dchwebb/DisPhaze/DisPhazePoly/src/LUT.cpp

#include "LUT.h"
#include "Calib.h"

extern Config config;

// Create phase distortion look up tables
const float PDSquareLUT[pdLutSize] = {0,0.000182,0.000446,0.000789,0.001206,0.001693,0.002248,0.002868,0.003549,0.004290,0.005087,0.005938,0.006841,0.007794,0.008795,0.009843,0.010935,0.012072,0.013250,0.014470,0.015730,0.017029,0.018366,0.019742,0.021155,0.022605,0.024091,0.025615,0.027175,0.028771,0.030405,0.032076,0.033786,0.035534,0.037322,0.039150,0.041021,0.042935,0.044895,0.046903,0.048960,0.051070,0.053237,0.055463,0.057754,0.060114,0.062551,0.065071,0.067684,0.070402,0.073238,0.082960,0.092174,0.100907,0.109182,0.117021,0.124446,0.131478,0.138135,0.144436,0.150398,0.156039,0.161373,0.166417,0.171183,0.175687,0.179939,0.183954,0.187742,0.191315,0.194682,0.197855,0.200842,0.203653,0.206296,0.208779,0.211110,0.213297,0.215346,0.217264,0.219058,0.220733,0.222295,0.223750,0.225102,0.226357,0.227520,0.228594,0.229584,0.230495,0.231329,0.232090,0.232783,0.233410,0.233974,0.234478,0.234926,0.235319,0.235660,0.235953,0.236198,0.236399,0.236557,0.236674,0.236753,0.236794,0.236800,0.236773,0.236713,0.236623,0.236503,0.236356,0.236182,0.235982,0.235758,0.235511,0.235242,0.234951,0.234640,0.234310,0.233961,0.233595,0.233211,0.232812,0.232396,0.231966,0.231522,0.231064,0.230593,0.230109,0.229614,0.229107,0.228589,0.228060,0.227521,0.226973,0.226415,0.225848,0.225272,0.224688,0.224096,0.223497,0.222890,0.222276,0.221655,0.221028,0.220394,0.219754,0.219108,0.218456,0.217799,0.217137,0.216469,0.215797,0.215120,0.214438,0.213751,0.213061,0.212366,0.211667,0.210964,0.210257,0.209547,0.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
9737,-0.060073,-0.060292,-0.060402,-0.060410,-0.060325,-0.060151,-0.059895,-0.059562,-0.059159,-0.058690,-0.058159,-0.057571,-0.056930,-0.056239,-0.055502,-0.054723,-0.053905,-0.053049,-0.052160,-0.051238,-0.050288,-0.049311,-0.048308,-0.047282,-0.046235,-0.045167,-0.044082,-0.042979,-0.041860,-0.040727,-0.039581,-0.038422,-0.037252,-0.036071,-0.034880,-0.033680,-0.032472,-0.031255,-0.030032,-0.028802,-0.027565,-0.026322,-0.025074,0};
const float PDSawLUT[pdLutSize] = {0.000248,-0.000447,-0.001176,-0.001876,-0.002599,-0.003271,-0.003971,-0.004643,-0.005344,-0.006067,-0.006795,-0.007547,-0.008247,-0.008947,-0.009647,-0.010371,-0.011098,-0.011799,-0.012522,-0.013250,-0.013978,-0.014702,-0.015457,-0.016158,-0.016909,-0.017608,-0.018310,-0.019060,-0.019789,-0.020544,-0.021267,-0.021967,-0.022696,-0.023447,-0.024203,-0.024954,-0.025682,-0.026408,-0.027105,-0.027860,-0.028589,-0.029340,-0.030096,-0.030847,-0.031602,-0.032330,-0.033081,-0.033837,-0.034588,-0.035343,-0.036072,-0.036850,-0.037607,-0.038385,-0.039140,-0.039890,-0.040617,-0.041346,-0.042098,-0.042880,-0.043639,-0.044443,-0.045198,-0.045727,-0.046478,-0.047235,-0.048016,-0.048825,-0.049602,-0.050359,-0.051136,-0.051893,-0.052676,-0.053455,-0.054236,-0.054990,-0.055799,-0.056578,-0.057361,-0.058137,-0.058894,-0.059673,-0.060455,-0.061234,-0.062019,-0.062823,-0.063606,-0.064384,-0.065169,-0.065974,-0.066759,-0.067560,-0.068317,-0.069095,-0.069877,-0.070658,-0.071469,-0.072275,-0.073086,-0.073892,-0.074700,-0.075481,-0.076284,-0.077069,-0.077873,-0.078660,-0.079492,-0.080299,-0.081080,-0.081893,-0.082725,-0.083535,-0.084341,-0.085147,-0.085960,-0.086795,-0.087634,-0.088464,-0.089267,-0.090052,-0.090858,-0.091668,-0.092477,-0.093315,-0.094149,-0.094980,-0.095790,-0.096599,-0.097434,-0.098243,-0.099074,-0.099890,-0.100749,-0.101580,-0.102389,-0.103198,-0.104036,-0.104867,-0.105680,-0.106513,-0.107348,-0.108189,-0.109043,-0.109857,-0.110723,-0.111581,-0.112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
611,0.057063,0.056451,0.055872,0.055259,0.054680,0.054069,0.053457,0.052877,0.052268,0.051626,0.051013,0.050430,0.049849,0.049238,0.048626,0.048016,0.047375,0.046736,0.046153,0.045565,0.044958,0.044347,0.043706,0.043427,0.042816,0.042174,0.041531,0.040918,0.040304,0.039691,0.039079,0.038436,0.037825,0.037156,0.036546,0.035875,0.035203,0.034561,0.033917,0.033304,0.032666,0.032024,0.031381,0.030740,0.030068,0.029426,0.028753,0.028117,0.027445,0.026774,0.026103,0.025432,0.024760,0.024092,0.023479,0.022806,0.022164,0.021492,0.020821,0.020155,0.019454,0.018782,0.018111,0.017439,0.016771,0.016128,0.015457,0.014785,0.014113,0.013418,0.012718,0.012046,0.011374,0.010679,0.010007,0.009335,0.008635,0.007935,0.007240,0.006511,0.005839,0.005168,0.004472,0.003800,0.003100,0.002372,0.001676,0.000977};
const float PDWave3LUT[pdLutSize] = {0.005028,0.005354,0.004452,0.003453,0.002683,0.001968,0.001094,0.000014,-0.001066,-0.002093,-0.003046,-0.004023,-0.005052,-0.006108,-0.007159,-0.008136,-0.009140,-0.010146,-0.011173,-0.012174,-0.013201,-0.014206,-0.015207,-0.016239,-0.017266,-0.018243,-0.019244,-0.020249,-0.021276,-0.022282,-0.023309,-0.024310,-0.025337,-0.026343,-0.027369,-0.028347,-0.029351,-0.030352,-0.031380,-0.032384,-0.033384,-0.034390,-0.035417,-0.036422,-0.037422,-0.038428,-0.039453,-0.040431,-0.041431,-0.042437,-0.043463,-0.044442,-0.045469,-0.046473,-0.047473,-0.048477,-0.049456,-0.050484,-0.051511,-0.052515,-0.053514,-0.054492,-0.055495,-0.056473,-0.057475,-0.058506,-0.059506,-0.060511,-0.061511,-0.062515,-0.063518,-0.064548,-0.065547,-0.066553,-0.067555,-0.068579,-0.069558,-0.070562,-0.071563,-0.072565,-0.073546,-0.074572,-0.075576,-0.076574,-0.077553,-0.078558,-0.079558,-0.080563,-0.081567,-0.082567,-0.083572,-0.084572,-0.085576,-0.086574,-0.087555,-0.088579,-0.089558,-0.090563,-0.091565,-0.092543,-0.093544,-0.094548,-0.095549,-0.096553,-0.097553,-0.098555,-0.099537,-0.100563,-0.101564,-0.102543,-0.103541,-0.104521,-0.105525,-0.106522,-0.107504,-0.108527,-0.109506,-0.110508,-0.111488,-0.112492,-0.113492,-0.114500,-0.115522,-0.116501,-0.117502,-0.118503,-0.119480,-0.120460,-0.121467,-0.122489,-0.123468,-0.124469,-0.125470,-0.126450,-0.127450,-0.128451,-0.129431,-0.130432,-0.131436,-0.132437,-0.133417,-0.134414,-0.135394,-0.136398,-0.137395,-0.138379,-0.139399,-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
,0.082001,0.081055,0.080078,0.079102,0.078127,0.077120,0.076142,0.075195,0.074221,0.073212,0.072238,0.071259,0.070314,0.069306,0.068359,0.067383,0.066408,0.065400,0.064455,0.063448,0.062472,0.061495,0.060519,0.059541,0.058594,0.057617,0.056641,0.055664,0.054688,0.053711,0.052734,0.051758,0.050780,0.049834,0.048828,0.047852,0.046875,0.045898,0.044922,0.043945,0.042970,0.041963,0.041017,0.040011,0.039033,0.038086,0.037109,0.036133,0.035156,0.034180,0.033202,0.032255,0.031279,0.030273,0.029297,0.028320,0.027344,0.026366,0.025419,0.024441,0.023517,0.022567,0.021449,0.019775,0.016492,0.009919,-0.001609,-0.019044,-0.041971,-0.068745,-0.097497,-0.126133,-0.151921,-0.169872,-0.172336,-0.158095,-0.134498,-0.107532,-0.080319,-0.054810,-0.032360,-0.014328,-0.001724,0.000977};
const float PDWave4LUT[pdLutSize] = {0.000594,0.000171,-0.000253,-0.000676,-0.001016,-0.001397,-0.001778,-0.002160,-0.002536,-0.002917,-0.003299,-0.003722,-0.004144,-0.004526,-0.004947,-0.005287,-0.005708,-0.006048,-0.006469,-0.006808,-0.007230,-0.007651,-0.007433,-0.007767,-0.008187,-0.008566,-0.008944,-0.009323,-0.009742,-0.010120,-0.010498,-0.010876,-0.011293,-0.011630,-0.012047,-0.012423,-0.012799,-0.013174,-0.013545,-0.013921,-0.014336,-0.014712,-0.015127,-0.015498,-0.015830,-0.016205,-0.016618,-0.016992,-0.017406,-0.017818,-0.018190,-0.018599,-0.018930,-0.019340,-0.019709,-0.020077,-0.020442,-0.020853,-0.021262,-0.021675,-0.022126,-0.022492,-0.022943,-0.023305,-0.023712,-0.024116,-0.023914,-0.024357,-0.024717,-0.025078,-0.025437,-0.025799,-0.026201,-0.026605,-0.027047,-0.027451,-0.027891,-0.028293,-0.028733,-0.029134,-0.029572,-0.029965,-0.030323,-0.030759,-0.031158,-0.031601,-0.032038,-0.032475,-0.032908,-0.033303,-0.033734,-0.034128,-0.034558,-0.034946,-0.035337,-0.035765,-0.036159,-0.036634,-0.037104,-0.037533,-0.037961,-0.038389,-0.038820,-0.039246,-0.039671,-0.040095,-0.040523,-0.040987,-0.041414,-0.041885,-0.042393,-0.042301,-0.042719,-0.043136,-0.043563,-0.044066,-0.044532,-0.045038,-0.045493,-0.045905,-0.046316,-0.046731,-0.047193,-0.047690,-0.048151,-0.048662,-0.049203,-0.049702,-0.050196,-0.050651,-0.051101,-0.051550,-0.052010,-0.052547,-0.053045,-0.053545,-0.054079,-0.054565,-0.055019,-0.055502,-0.055943,-0.056396,-0.056933,-0.057472,-0.058007,-0.058541,-0.05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
0.030631,0.030337,0.029941,0.029596,0.029202,0.028803,0.028461,0.028062,0.027713,0.027312,0.026965,0.026516,0.026161,0.025808,0.025404,0.025047,0.024686,0.024374,0.024014,0.024272,0.023862,0.023549,0.023140,0.022782,0.022418,0.022054,0.021689,0.021324,0.020955,0.020630,0.020354,0.019986,0.019620,0.019206,0.018840,0.018515,0.018141,0.017861,0.017490,0.017118,0.016744,0.016415,0.016090,0.015759,0.015429,0.015097,0.014768,0.014391,0.014060,0.013685,0.013314,0.012937,0.012603,0.012269,0.011932,0.011686,0.011312,0.010979,0.010556,0.010219,0.009926,0.009589,0.009294,0.009603,0.009222,0.008885,0.008547,0.008208,0.007918,0.007581,0.007200,0.006819,0.006438,0.006099,0.005802,0.005510,0.005171,0.004833,0.004451,0.004112,0.003730,0.003391,0.003098,0.002803,0.001953,0.000977};
const float PDWave5LUT[pdLutSize] = {0.002996,0.005019,0.007045,0.009074,0.011107,0.013145,0.015191,0.020278,0.022350,0.024432,0.026528,0.028637,0.030761,0.032902,0.035061,0.037239,0.039439,0.041662,0.043910,0.046184,0.048488,0.050822,0.053190,0.059010,0.061495,0.064025,0.066603,0.069234,0.071922,0.074671,0.077488,0.080377,0.083347,0.086405,0.089559,0.092821,0.096201,0.099715,0.103378,0.112215,0.116474,0.121001,0.125851,0.131099,0.136849,0.143264,0.150217,0.149538,0.155373,0.159080,0.156494,0.152900,0.149978,0.147383,0.144327,0.138182,0.135051,0.131985,0.129052,0.126016,0.122975,0.119990,0.117197,0.114451,0.111810,0.109067,0.106428,0.103880,0.101310,0.098820,0.094885,0.092415,0.090016,0.087637,0.085281,0.083001,0.080680,0.078424,0.076134,0.073913,0.071711,0.069515,0.067336,0.065215,0.063066,0.060965,0.057732,0.055661,0.053563,0.051515,0.049474,0.047443,0.045435,0.043508,0.041503,0.039545,0.037555,0.035621,0.033687,0.031759,0.029837,0.027922,0.025135,0.023235,0.021345,0.019502,0.017663,0.015792,0.013997,0.012135,0.010353,0.008545,0.006770,0.004964,0.003196,0.001393,-0.000396,-0.002149,-0.004711,-0.006454,-0.008194,-0.009926,-0.011655,-0.013350,-0.015074,-0.016758,-0.018440,-0.020155,-0.021833,-0.023513,-0.025221,-0.026890,-0.028553,-0.030941,-0.032567,-0.034226,-0.035878,-0.037488,-0.039107,-0.040754,-0.042369,-0.044012,-0.045623,-0.047252,-0.048821,-0.050423,-0.052018,-0.053583,-0.055180,-0.057350,-0.058937,-0.060495,-0.062080,-0.063630,-0.065174,-0.066722,-0.068275,-0.069847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
02720,-0.003114,-0.003760,-0.004447,-0.005096,-0.005742,-0.006436,-0.007088,-0.007701,-0.008313,-0.008964,-0.009615,-0.010264,-0.010951,-0.011641,-0.012295,-0.012558,-0.013173,-0.013826,-0.014482,-0.015100,-0.015716,-0.016373,-0.016994,-0.017576,-0.018194,-0.018858,-0.019442,-0.020064,-0.020650,-0.021234,-0.021856,-0.022090,-0.022714,-0.023307,-0.023895,-0.024484,-0.025072,-0.025699,-0.026252,-0.026843,-0.027398,-0.027989,-0.028550,-0.029140,-0.029769,-0.030325,-0.030953,-0.031200,-0.031722,-0.032317,-0.032881,-0.033475,-0.034113,-0.034319,-0.032140,-0.029981,-0.027840,-0.025716,-0.023607,-0.021512,-0.019429,-0.017357,-0.015296,-0.010225,-0.008186,-0.006153,-0.004124,-0.002099,-0.000075,0.001953,0.000977};

// naive resonant wave six at 100% (x16 sine waves per cycle)
const float PDWave6_100LUT[pdLutSize] = {-0.002294,-0.008418,-0.015106,-0.022301,-0.029950,-0.038008,-0.046454,-0.055302,-0.073145,-0.082913,-0.092824,-0.102859,-0.113041,-0.123406,-0.133827,-0.144362,-0.154953,-0.165490,-0.176008,-0.186217,-0.196130,-0.205461,-0.214116,-0.221596,-0.230461,-0.231320,-0.229609,-0.225584,-0.220020,-0.213345,-0.205917,-0.197929,-0.189600,-0.181006,-0.172185,-0.163249,-0.154450,-0.145749,-0.137217,-0.128739,-0.120341,-0.102871,-0.094903,-0.087138,-0.079649,-0.072485,-0.065730,-0.059436,-0.053530,-0.048064,-0.043023,-0.038470,-0.034445,-0.031010,-0.028194,-0.026070,-0.024669,-0.023020,-0.023776,-0.025215,-0.027379,-0.030294,-0.033866,-0.038088,-0.042917,-0.048310,-0.054192,-0.060552,-0.067372,-0.074605,-0.082242,-0.090207,-0.098504,-0.106972,-0.123263,-0.132026,-0.140849,-0.149715,-0.158618,-0.167512,-0.176257,-0.184766,-0.192869,-0.200494,-0.207626,-0.214261,-0.220275,-0.225507,-0.229790,-0.233009,-0.235110,-0.234954,-0.233757,-0.231509,-0.228378,-0.224358,-0.219633,-0.214171,-0.208253,-0.201997,-0.195479,-0.188820,-0.181991,-0.175014,-0.167903,-0.160695,-0.153514,-0.138350,-0.131525,-0.124967,-0.118668,-0.112656,-0.106899,-0.101454,-0.096402,-0.091757,-0.087548,-0.083862,-0.080729,-0.078285,-0.076475,-0.075261,-0.074684,-0.074660,-0.076194,-0.078449,-0.081352,-0.084858,-0.088957,-0.093640,-0.098864,-0.104590,-0.110749,-0.117309,-0.124208,-0.131432,-0.138895,-0.146540,-0.154364,-0.162309,-0.177421,-0.185501,-0.193585,-0.201609,-0.209480,-0.217094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
6333,0.095448,0.094596,0.093827,0.093103,0.092448,0.091822,0.091221,0.090680,0.090157,0.089674,0.089195,0.088729,0.088821,0.088372,0.087928,0.087471,0.087005,0.086511,0.086003,0.085461,0.084925,0.084368,0.083741,0.083112,0.082366,0.081638,0.080857,0.080045,0.079176,0.078316,0.077332,0.076302,0.075217,0.074133,0.073023,0.071826,0.070608,0.069395,0.068175,0.066921,0.065637,0.064358,0.063085,0.061794,0.060472,0.058887,0.057593,0.056319,0.055069,0.053833,0.052601,0.051397,0.050226,0.049085,0.047947,0.046829,0.045734,0.044653,0.043605,0.042604,0.041628,0.040632,0.039683,0.038743,0.037827,0.036931,0.036048,0.035161,0.034283,0.033396,0.032519,0.031641,0.030758,0.029890,0.029004,0.028093,0.027183,0.026249,0.025121,0.023738,0.021881,0.019347,0.016071,0.012041,0.007329,0.002019,0.000977};
const float PDWave6_50LUT[pdLutSize] = {-5.1e-05,-0.001103,-0.002173,-0.003262,-0.004412,-0.005585,-0.006895,-0.008368,-0.010076,-0.012032,-0.014737,-0.017139,-0.019832,-0.022719,-0.025766,-0.028999,-0.033341,-0.037103,-0.041043,-0.044961,-0.049152,-0.053482,-0.059063,-0.063672,-0.068435,-0.073244,-0.078207,-0.083378,-0.090039,-0.095325,-0.100624,-0.106132,-0.111689,-0.11728,-0.123149,-0.130749,-0.136514,-0.142306,-0.148096,-0.154164,-0.16005,-0.16781,-0.174216,-0.180201,-0.18631,-0.192289,-0.198306,-0.205892,-0.211736,-0.217586,-0.223639,-0.229306,-0.234679,-0.241439,-0.246334,-0.250682,-0.254757,-0.258527,-0.261657,-0.264475,-0.265613,-0.265961,-0.265628,-0.264307,-0.262754,-0.260424,-0.256342,-0.253248,-0.249701,-0.245962,-0.242096,-0.237908,-0.231964,-0.227588,-0.223127,-0.21854,-0.214026,-0.209483,-0.203092,-0.198494,-0.193835,-0.189152,-0.184485,-0.179666,-0.173082,-0.168389,-0.163751,-0.159114,-0.15446,-0.149795,-0.143242,-0.138489,-0.133938,-0.129432,-0.124963,-0.120517,-0.116074,-0.109926,-0.105532,-0.101015,-0.096779,-0.092626,-0.088703,-0.083036,-0.079098,-0.075261,-0.071542,-0.06767,-0.06398,-0.059144,-0.055807,-0.052696,-0.049896,-0.047003,-0.044211,-0.040253,-0.037922,-0.035732,-0.033697,-0.031921,-0.030407,-0.029092,-0.027224,-0.026243,-0.025692,-0.025388,-0.025336,-0.02551,-0.025859,-0.026734,-0.027831,-0.029132,-0.030676,-0.032551,-0.035097,-0.037594,-0.040229,-0.04317,-0.046271,-0.049682,-0.053995,-0.057782,-0.061612,-0.06569,-0.069872,-0.074174,-0.07971,-0.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
84,0.06469,0.063504,0.062335,0.061166,0.059965,0.058919,0.057863,0.056801,0.055753,0.054785,0.053788,0.05278,0.051879,0.050929,0.050052,0.049182,0.048326,0.047524,0.046749,0.045908,0.045095,0.044334,0.043569,0.042901,0.042139,0.041397,0.040702,0.03996,0.039269,0.038678,0.037911,0.037243,0.036577,0.035843,0.035189,0.034597,0.033882,0.033211,0.032521,0.031802,0.031064,0.03041,0.029677,0.028972,0.028267,0.027488,0.026774,0.025999,0.025279,0.024529,0.023706,0.022926,0.0221,0.021235,0.020433,0.019539,0.018727,0.01784,0.016948,0.016046,0.01514,0.014206,0.013191,0.012238,0.011299,0.010384,0.00936,0.008332,0.007342,0.00629,0.005257,0.004215,0.00314,0.002051,0.001051};

// Create an array of pointers to the PD LUTs
const float* LUTArray[7] = { PDSquareLUT, PDWave4LUT, PDWave5LUT, PDSawLUT, PDWave3LUT, PDWave6_100LUT, PDWave6_50LUT };

// FIXME - temporary
#define ADDR_FLASH_SECTOR_6    reinterpret_cast<float*>(0x08040000)		// Base address of Sector 6, 128 Kbytes
constexpr float midiLUTFirstNote = 21.0f;			// 21 = 27.5Hz (A0)
constexpr float midiLUTNotes = 100.0f;				// 121 = 8869.84Hz (C#9)
constexpr uint32_t midiLUTSize = 16384;				// Size of MIDI to pitch LUT
//float* MidiLUT = ADDR_FLASH_SECTOR_6;

float* MidiLUT = reinterpret_cast<float*>(0x10000000);	// Put LUT in CCRAM
float SineLUT[sinLutSize];
//float* SineLUT = reinterpret_cast<float*>(0x10000000);	// Put sine LUT in CCRAM


void CreateLUTs()
{
	// Generate Sine LUT
	for (uint32_t s = 0; s < sinLutSize; ++s) {
		SineLUT[s] = sin(s * 2.0f * M_PI / sinLutSize);
	}

	constexpr float mult = std::pow(2.0f, 32.0f) / sampleRatePoly;
	for (uint32_t i = 0; i < midiLUTSize; ++i) {
		float n = midiLUTFirstNote + ((float)i / (float)midiLUTSize) * midiLUTNotes;
		MidiLUT[i] = (440.0f * std::pow(2.0f, (n - 69.0f) / 12.0f)) * mult;			// 69 is midi note of A 440
	}
}
