dchwebb/DisPhaze/DisPhaze/src/PhaseDistortion.cpp

#include "PhaseDistortion.h"

extern	bool dacRead;
extern volatile uint32_t debugWorkTime, debugInterval;

PhaseDistortion phaseDist;


inline float PhaseDistortion::sinLutWrap(float pos)
{
	while (pos >= SINLUTSIZE) {
		pos -= SINLUTSIZE;
	}
	while (pos < 0) {
		pos =  SINLUTSIZE + pos;
	}
	return pos;
}

//	Interpolate between two positions (derived from a float and its rounded value) in a LUT
float PhaseDistortion::Interpolate(float* LUT, float& LUTPosition)
{
	const float s1 = LUT[static_cast<int32_t>(LUTPosition)];
	const float s2 = LUT[static_cast<int32_t>(LUTPosition + 1) % LUTSIZE];
	return s1 + ((s2 - s1) * (LUTPosition - std::round(LUTPosition)));
}


// Generate a phase distorted sine wave - pass LUT containing PD offsets, LUT position as a fraction of the wave cycle and a scaling factor
float PhaseDistortion::GetPhaseDist(const float* PdLUT, const float LUTPosition, const float scale)
{
	const float phaseDist = PdLUT[static_cast<int32_t>(LUTPosition * LUTSIZE)] * SINLUTSIZE * scale;

	// Add main wave position to phase distortion position and ensure in bounds
	const float pos = sinLutWrap((LUTPosition * SINLUTSIZE) + phaseDist);

	return SineLUT[static_cast<uint32_t>(pos)];
}


float PhaseDistortion::GetResonantWave(const float LUTPosition, float scale)
{
	// models waves 6-8 of the Casio CZ which are saw/triangle envelopes into which harmonics are added as the phase distortion increases
	scale = ((scale / 5.0f) * 23.0f) + 1.0f;		// Sets number of sine waves per cycle: scale input 0-5 to 1-24 (original only went to 16)

	// offset to 3/4 of the way through the sine wave so each cycle starts at the flat top of the wave
	constexpr float sineOffset = static_cast<float>(3 * (SINLUTSIZE / 4));

	const float pos = sinLutWrap(((LUTPosition * SINLUTSIZE) * scale) + sineOffset);

	// Scale the amplitude of the cycle from 1 to 0 to create a saw tooth type envelope on each cycle
	float ampMod = 1.0f;
	if (pdLut2 == 5) {								// Saw tooth - amplitude linearly reduces over full cycle
		ampMod = (1.0f - LUTPosition);
	} else if (LUTPosition > 0.5f) {				// Both triangle (wave 7) and loud saw (wave 8) fade out over second half of cycle
		ampMod = (2.0f * (1.0f - LUTPosition));
	} else if (pdLut2 == 6) {						// Triangle (wave 7) fades in over first half of cycle
		ampMod = (LUTPosition * 2.0f);
	}

	float sineSample = SineLUT[static_cast<uint32_t>(pos)];
	sineSample = (sineSample + 1.0f) * ampMod;		// Offset so all positive and then apply amplitude envelope to create sawtooth

	lastSample = (lastSample * 0.85f) + (0.15f * (sineSample - 1.0f));			// Remove offset and damp
	return lastSample;
}



// Generate a phase distorted sine wave - pass LUT containing PD offsets, LUT position as a fraction of the wave cycle and a scaling factor
float PhaseDistortion::GetBlendPhaseDist(const float pdBlend, const float LUTPosition, const float scale)
{
	// Get the two PD LUTs that will be blended
	const float* pdLUTBlendA = LUTArray[static_cast<uint8_t>(pdBlend)];
	const float* pdLUTBlendB = LUTArray[static_cast<uint8_t>(pdBlend + 1) % pd1LutCount];

	// Get the values from each LUT for the sample position
	const float phaseDistA = pdLUTBlendA[(int)(LUTPosition * LUTSIZE)] * SINLUTSIZE * scale;
	const float phaseDistB = pdLUTBlendB[(int)(LUTPosition * LUTSIZE)] * SINLUTSIZE * scale;

	// Get the weighted blend of the two PD amounts
	const float blend = pdBlend - (uint8_t)pdBlend;
	const float phaseDist = ((1 - blend) * phaseDistA) + (blend * phaseDistB);

	// Add main wave position to phase distortion position and ensure in bounds
	const float pos = sinLutWrap((LUTPosition * SINLUTSIZE) + phaseDist);

	return SineLUT[static_cast<uint32_t>(pos)];
}


void PhaseDistortion::CalcNextSamples()
{
	// Around the center point of the ADC the reading averages to the low side causing tuning problems - adjust here
	uint16_t adjPitch = ADC_array[ADC_Pitch];
	if (adjPitch == 2047) {
		adjPitch += centerPitchAdj;
	}

	// Calculate frequencies
	pitch = ((3 * pitch) + adjPitch) / 4;							// 1V/Oct input with smoothing
	fineTune = ((15 * fineTune) + ADC_array[ADC_FTune]) / 16;		// Fine tune with smoothing
	freq1 = PitchLUT[pitch + ((2048 - fineTune) / 32)];

	//	Coarse tuning - add some hysteresis to prevent jumping
	if (coarseTune > ADC_array[ADC_CTune] + 128 || coarseTune < ADC_array[ADC_CTune] - 128) {
		coarseTune = ADC_array[ADC_CTune];
	}
	if (coarseTune > 3412) {
		freq1 *= 4;
	} else if (coarseTune > 2728) {
		freq1 *= 2;
	} else if (coarseTune < 682) {
		freq1 /= 4;
	} else if (coarseTune < 1364) {
		freq1 /= 2;
	}


	// octave down
	switch (relativePitch) {
		case NONE: 			freq2 = freq1; 			break;
		case OCTAVEDOWN:	freq2 = freq1 / 2.0f;	break;
		case OCTAVEUP: 		freq2 = freq1 * 2.0f;	break;
	}

	// jump forward to the next sample position
	samplePos1 += freq1;
	while (samplePos1 >= SAMPLERATE) {
		samplePos1 -= SAMPLERATE;
	}

	samplePos2 += freq2;
	while (samplePos2 >= SAMPLERATE) {
		samplePos2 -= SAMPLERATE;
	}

	// Analog selection of PD LUT table allows a smooth transition between LUTs for DAC1 and a stepped transition for DAC2
	pd1Type = ((31 * pd1Type) + ADC_array[ADC_Osc1Type]) / 32;
	pdLut1 = static_cast<float>(pd1Type * (pd1LutCount - 1)) / 4096.0f;

	// Apply hysteresis on PD 2 discrete LUT selector
	if (pd2Type > ADC_array[ADC_Osc2Type] + 128 || pd2Type < ADC_array[ADC_Osc2Type] - 128) {
		pd2Type = ADC_array[ADC_Osc2Type];
	}
	pdLut2 = pd2Type * pd2LutCount / 4096;
	pd2Resonant = (pdLut2 > 4);


	// Get PD amount from pot and CV ADCs; Currently seeing 0v as ~3000 and 5V as ~960 (converted to 0.0f - 5.0f)
	const float tmpPD1Scale = static_cast<float>(std::min((3800 - ADC_array[ADC_PD1CV]) + ADC_array[ADC_PD1Pot], 5000)) / 1000.0f;	// Convert PD amount for OSC1
	pd1Scale = std::max(((pd1Scale * 31) + tmpPD1Scale) / 32, 0.0f);

	const float tmpPD2Scale = static_cast<float>(std::min((4096 - ADC_array[ADC_PD2CV]) + ADC_array[ADC_PD2Pot], 5000)) / 1000.0f;	// Convert PD amount for OSC2
	if (pd2Resonant) {
		pd2Scale = (pd2Scale * 0.995f) + (tmpPD2Scale * 0.005f);		// Heavily damp PD2 scale if using resonant waves to reduce jitter noise
	} else {
		pd2Scale = ((pd2Scale * 31) + tmpPD2Scale) / 32;
	}


	// Get VCA levels (filtering out very low level VCA signals)
	if (ADC_array[ADC_VCA] > 4070) {
		VCALevel = 0;
	} else if (ADC_array[ADC_VCA] < 30) {
		VCALevel = 1;
	} else {
		VCALevel = ((VCALevel * 31) + (4096.0f - ADC_array[ADC_VCA]) / 4096) / 32;			// Convert ADC for VCA to float between 0 and 1 with damping
	}

	// Calculate output as a float from -1 to +1 checking phase distortion and phase offset as required
	const float sampleOut1 = GetBlendPhaseDist(pdLut1, samplePos1 / SAMPLERATE, pd1Scale);

	float sampleOut2;
	if (pd2Resonant) {
		sampleOut2 = GetResonantWave(samplePos2 / SAMPLERATE, pd2Scale);
	} else {
		sampleOut2 = GetPhaseDist(LUTArray[pdLut2], samplePos2 / SAMPLERATE, pd2Scale);
	}

	// Set DAC output values for when sample interrupt next fires
	if (ringModOn) {
		DAC->DHR12R1 = static_cast<int32_t>((1 + (sampleOut1 * sampleOut2) * VCALevel) * 2047);			// Ring mod of 1 * 2
	} else {
		DAC->DHR12R1 = static_cast<int32_t>((1 + sampleOut1 * VCALevel) * 2047);
	}
	if (mixOn) {
		DAC->DHR12R2 = static_cast<int32_t>(((2 + (sampleOut1 + sampleOut2) * VCALevel) / 2) * 2047);	// Mix of 1 + 2
	} else {
		DAC->DHR12R2 = static_cast<int32_t>((1 + sampleOut2 * VCALevel) * 2047);
	}

	dacRead = 0;		// Clear ready for next sample flag
}
