dchwebb/DisPhaze/DisPhazePoly/src/LUT.h

#pragma once

#include "initialisation.h"
#include "configManager.h"
#include <cmath>

// LUT sizes are probably all going to be constant
static constexpr uint32_t pdLutSize = 1024;
static constexpr uint32_t sinLutSize = 16384;

extern const float PDSquareLUT[pdLutSize];
extern const float PDSawLUT[pdLutSize];
extern const float PDWave3LUT[pdLutSize];
extern const float PDWave4LUT[pdLutSize];
extern const float PDWave5LUT[pdLutSize];

// Create an array of pointers to the PD LUTs
extern const float* LUTArray[7];

extern float SineLUT[sinLutSize];
//extern float* SineLUT;
extern const uint32_t midiLUTSize;
extern float* MidiLUT;
extern const float midiLUTFirstNote;
extern const float midiLUTNotes;

void CreateLUTs();
